ericw6408/bintarboard/datasheets/keyboard-layout.png

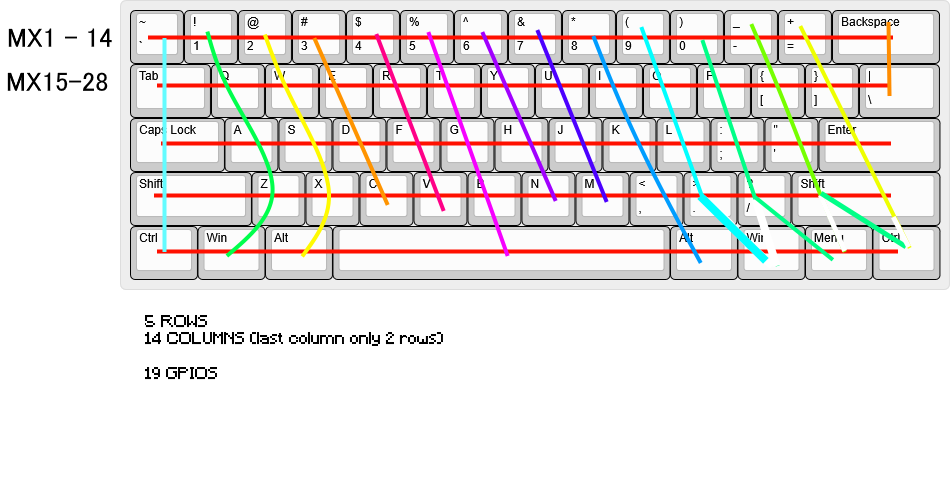
datasheets/keyboard-layout.png
