ericw6408/bintarboard/demo/3d design photo/bintarboard plate.png

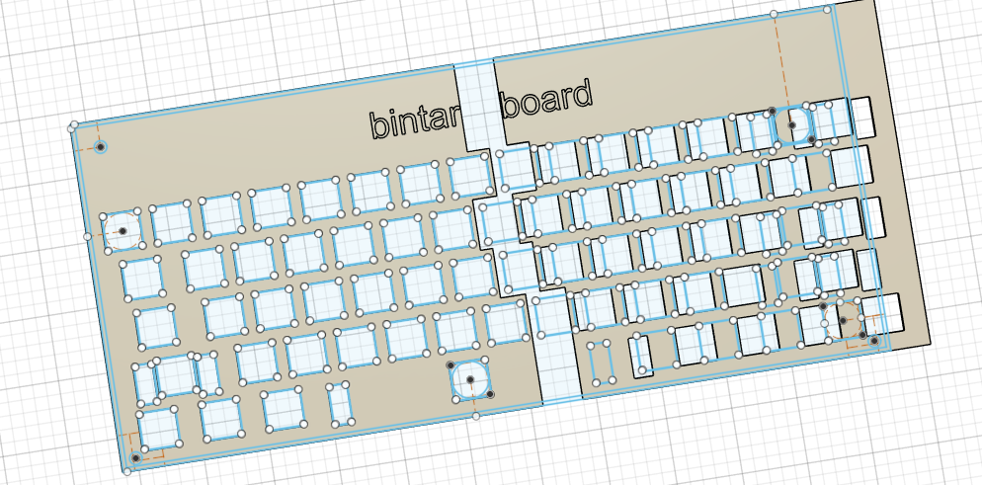
demo/3d design photo/bintarboard plate.png
