ericw6408/bintarboard/demo/pcb and schematic photo/keyboard matrix schematic.png

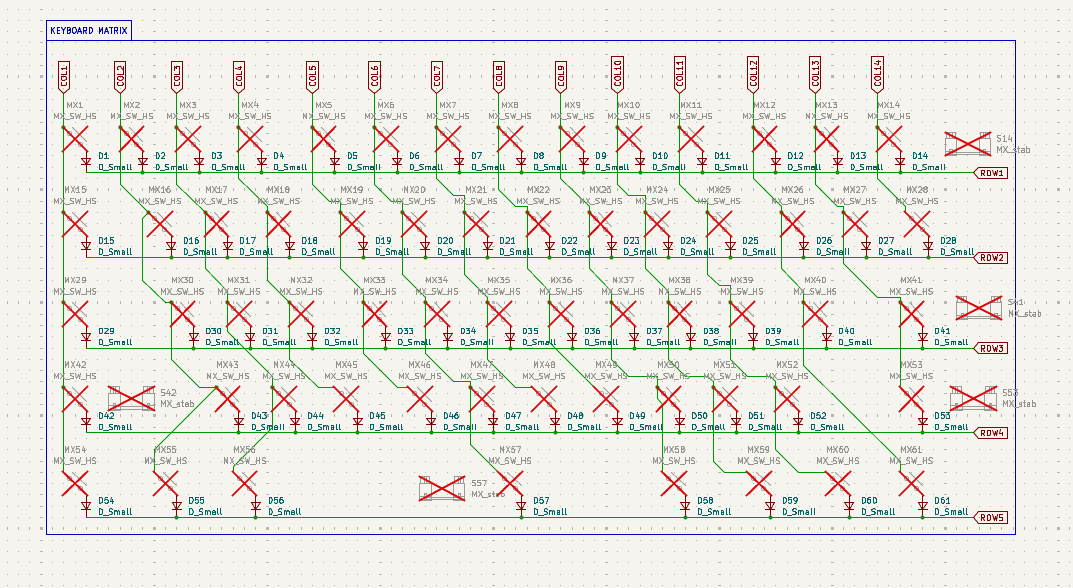
demo/pcb and schematic photo/keyboard matrix schematic.png
