ericw6408/bintarboard/demo/pcb and schematic photo/PCB.png

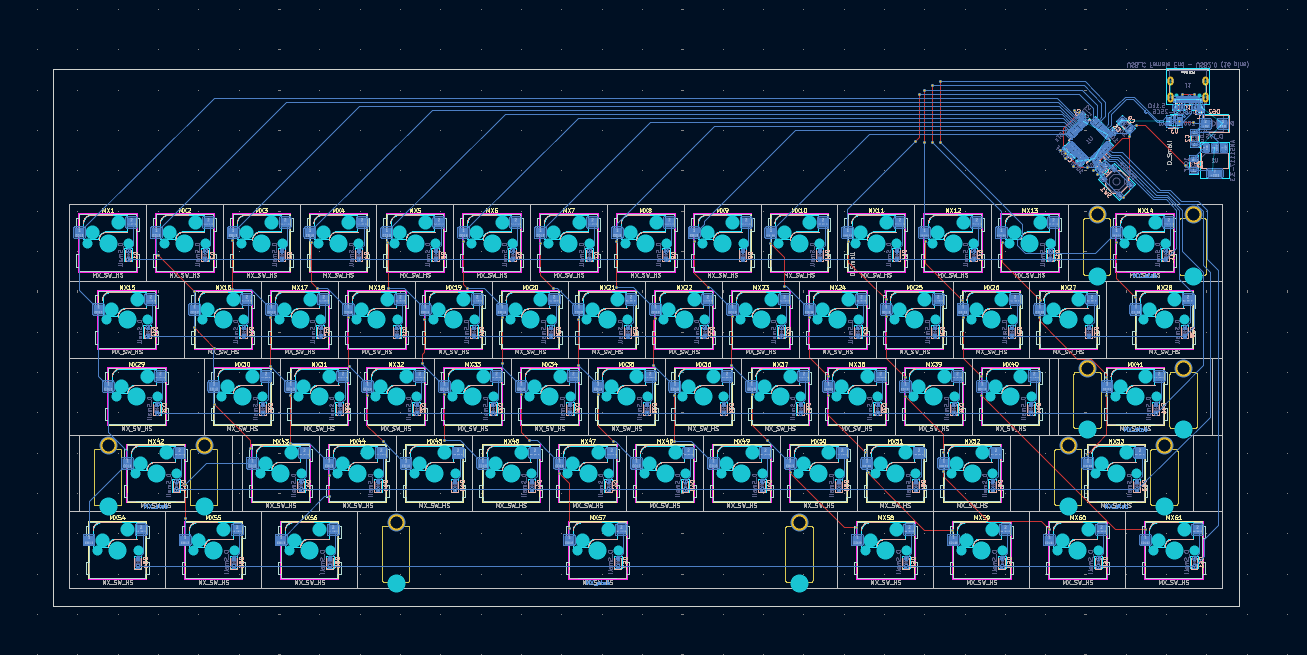
demo/pcb and schematic photo/PCB.png
